MBuzbuchi/TSC_PROJ_1/images/OpenBook_Enclosure_2025-Apr-06_09-24-30PM-000_CustomizedView9800252469.png

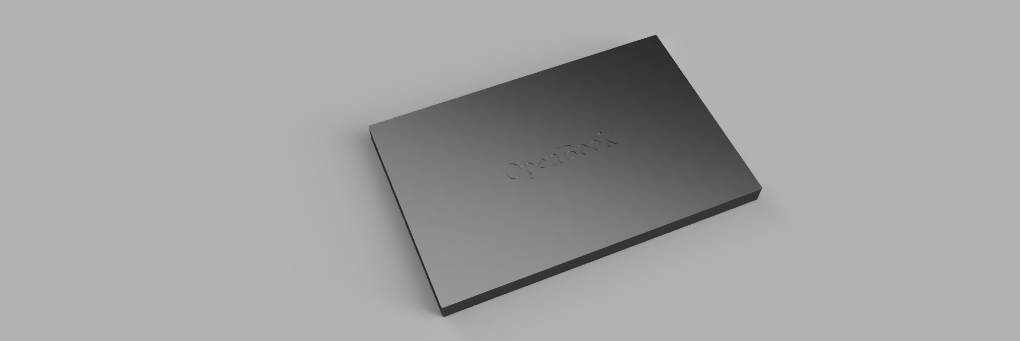
images/OpenBook_Enclosure_2025-Apr-06_09-24-30PM-000_CustomizedView9800252469.png
