MBuzbuchi/TSC_PROJ_1/images/OpenBook_Enclosure_2025-Apr-06_09-27-13PM-000_CustomizedView309341721.png

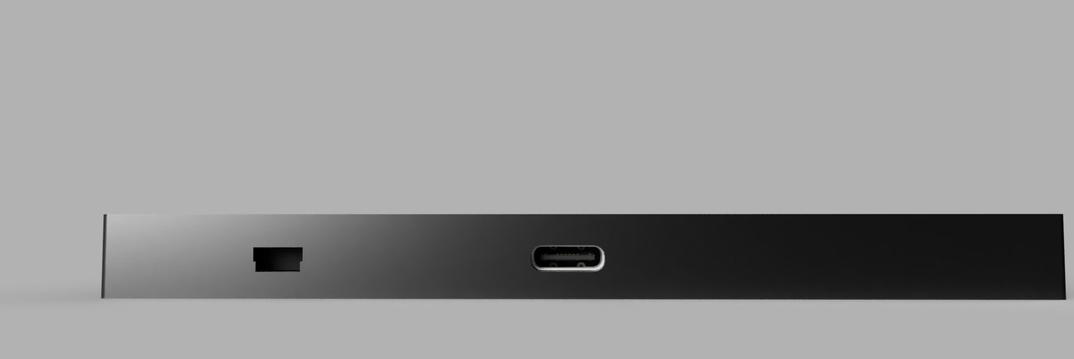
images/OpenBook_Enclosure_2025-Apr-06_09-27-13PM-000_CustomizedView309341721.png
