MBuzbuchi/TSC_PROJ_1/images/PCB_E_BOOK_v1_2025-Apr-06_09-19-52PM-000_CustomizedView14307804733.png

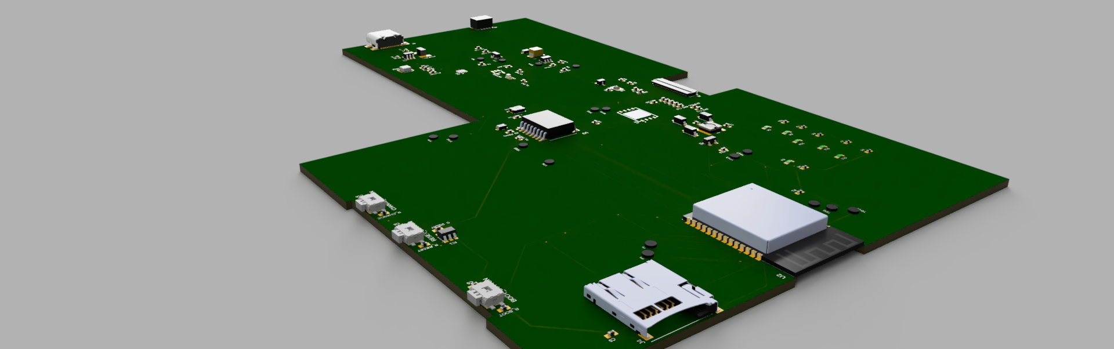
images/PCB_E_BOOK_v1_2025-Apr-06_09-19-52PM-000_CustomizedView14307804733.png
